ocularb0b/le3p/stls/manufactured/export_GantryCIdlers.stl

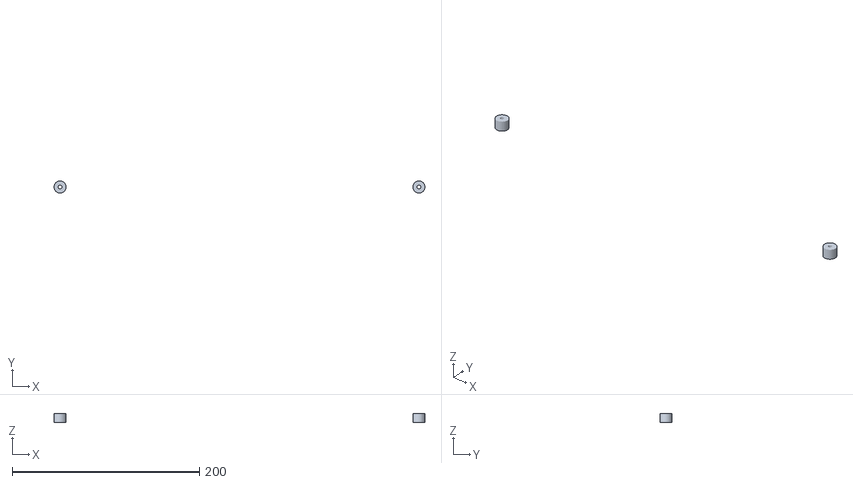
[picture p15: CAD file, 2014-03-09]
stls/manufactured/export_GantryCIdlers.stl
396.0 x 13.0 x 10.0
