ocularb0b/le3p/stls/printed/export_XCarriage.stl

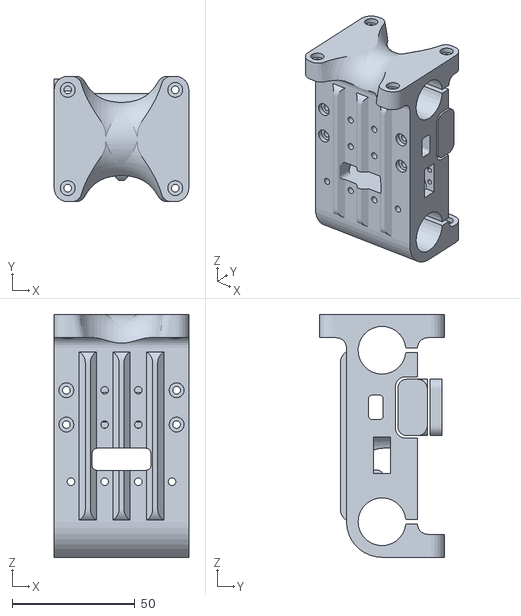
[picture p16: CAD file, 2014-02-16]
stls/printed/export_XCarriage.stl
55.0 x 51.2 x 99.2
