ocularb0b/le3p/stls/manufactured/export_GantryXBushings.stl

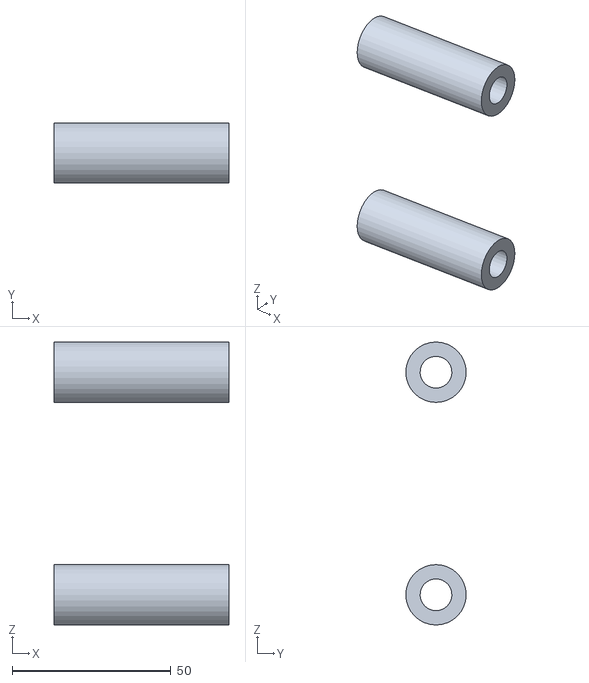
[picture p17: CAD file, 2014-03-09]
stls/manufactured/export_GantryXBushings.stl
55.0 x 19.0 x 89.0
