ocularb0b/le3p/stls/printed/export_XEnds.stl

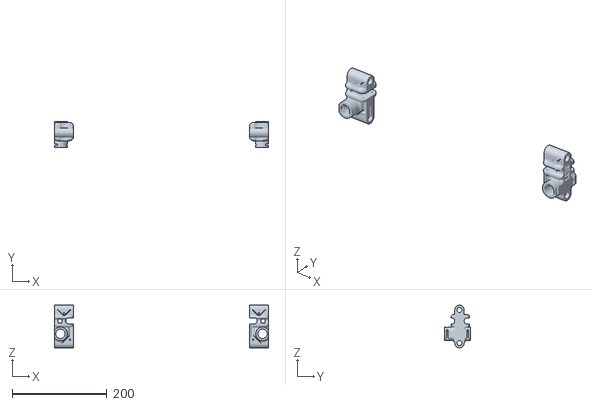
[picture p18: CAD file, 2014-02-16]
stls/printed/export_XEnds.stl
451.0 x 55.0 x 90.0
