ocularb0b/le3p/stls/manufactured/export_GantryMotors.stl

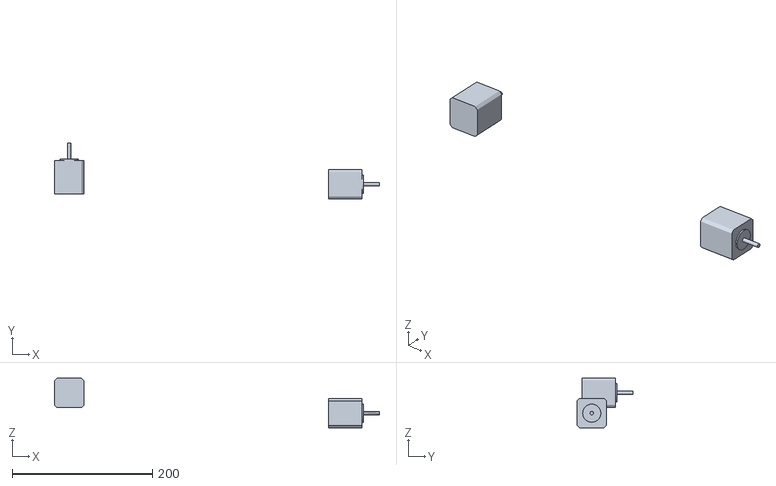
[picture p19: CAD file, 2014-03-09]
stls/manufactured/export_GantryMotors.stl
463.5 x 79.8 x 71.0
