ocularb0b/le3p/stls/printed/forprint_YEndsMotor.stl

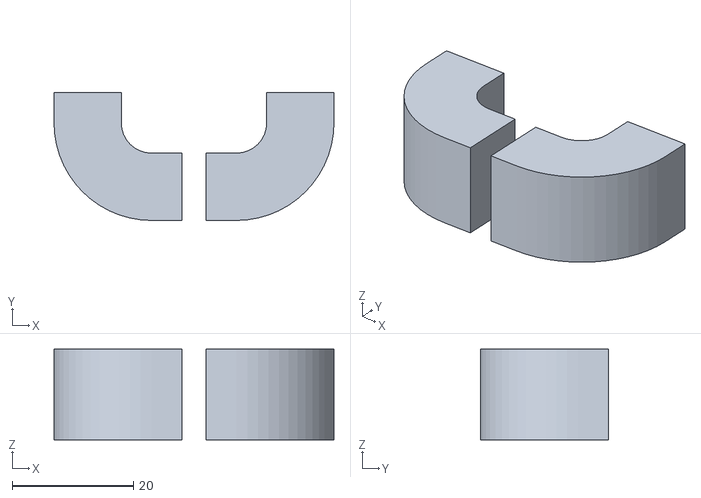
[picture p20: CAD file, 2013-11-06]
stls/printed/forprint_YEndsMotor.stl
46.2 x 21.1 x 15.0
