ocularb0b/le3p/stls/manufactured/export_GantryXRods.stl

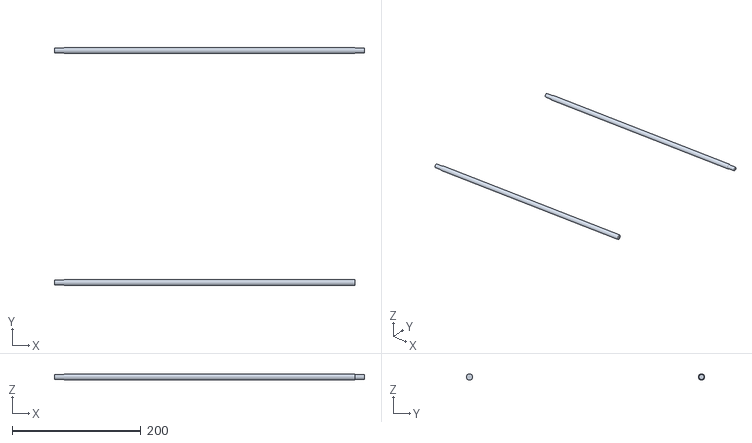
[picture p21: CAD file, 2014-03-09]
stls/manufactured/export_GantryXRods.stl
481.0 x 370.0 x 9.96
