ocularb0b/le3p/stls/printed/forprint_NozzleFanShroud.stl

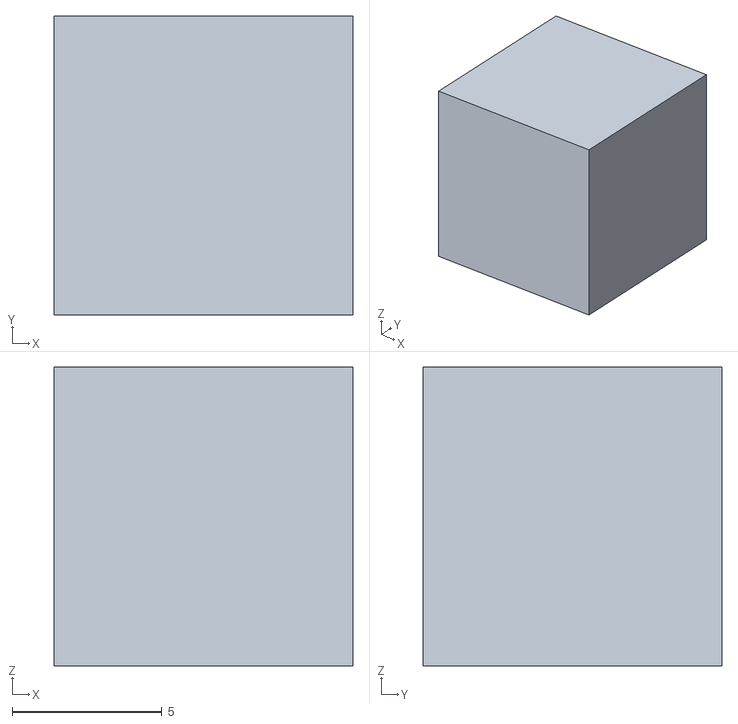
[picture p22: CAD file, 2013-11-01]
stls/printed/forprint_NozzleFanShroud.stl
10.0 x 10.0 x 10.0
