ocularb0b/le3p/stls/manufactured/export_ExtruderIdleBearing.stl

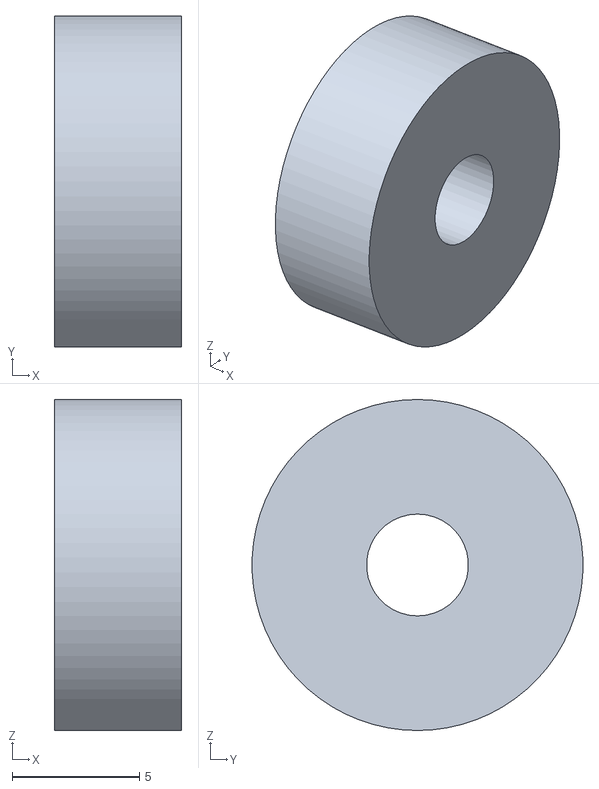
[picture p23: CAD file, 2014-03-09]
stls/manufactured/export_ExtruderIdleBearing.stl
5.00 x 13.0 x 13.0
