ocularb0b/le3p/stls/printed/export_DimmerMount.stl

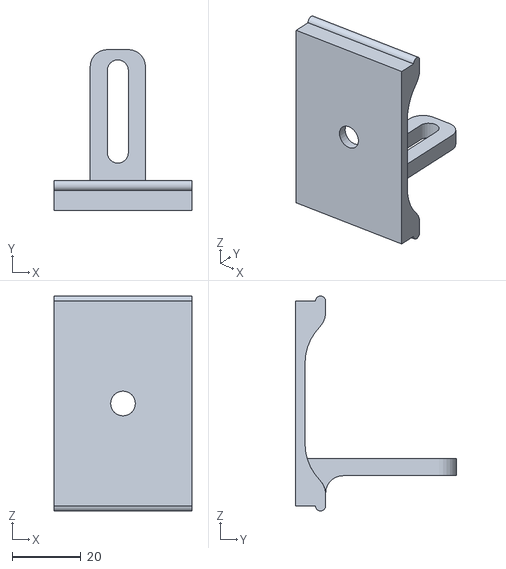
[picture p24: CAD file, 2013-10-20]
stls/printed/export_DimmerMount.stl
40.0 x 46.8 x 62.5
