ocularb0b/le3p/stls/manufactured/export_ExtruderDriveGear.stl

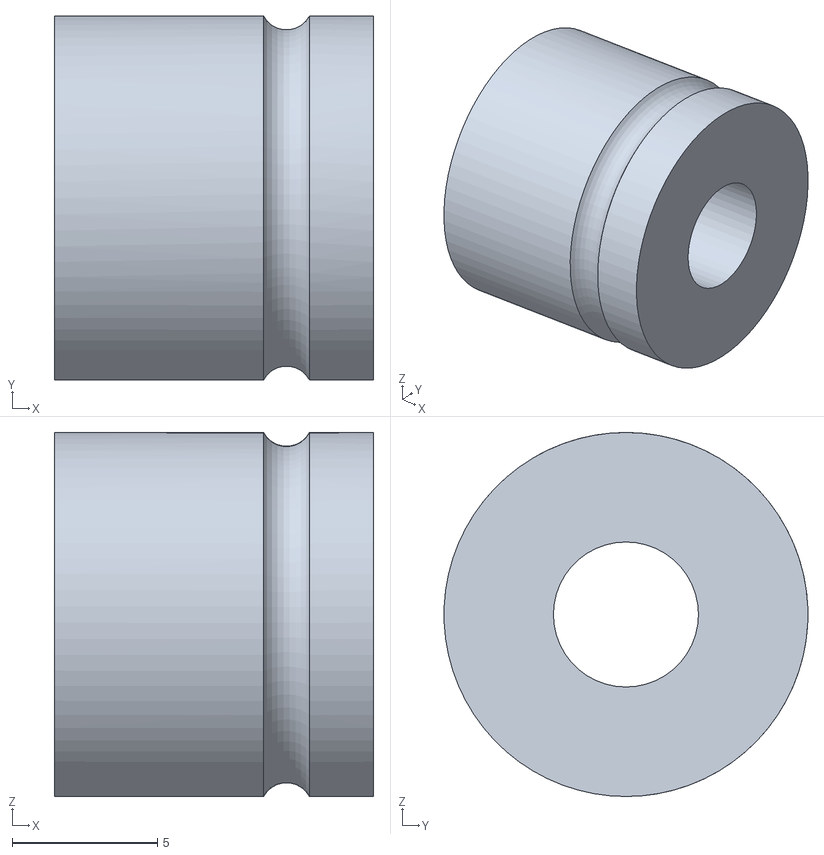
[picture p25: CAD file, 2014-03-09]
stls/manufactured/export_ExtruderDriveGear.stl
11.0 x 12.5 x 12.6
