ocularb0b/le3p/stls/printed/export_ControllerArm.stl

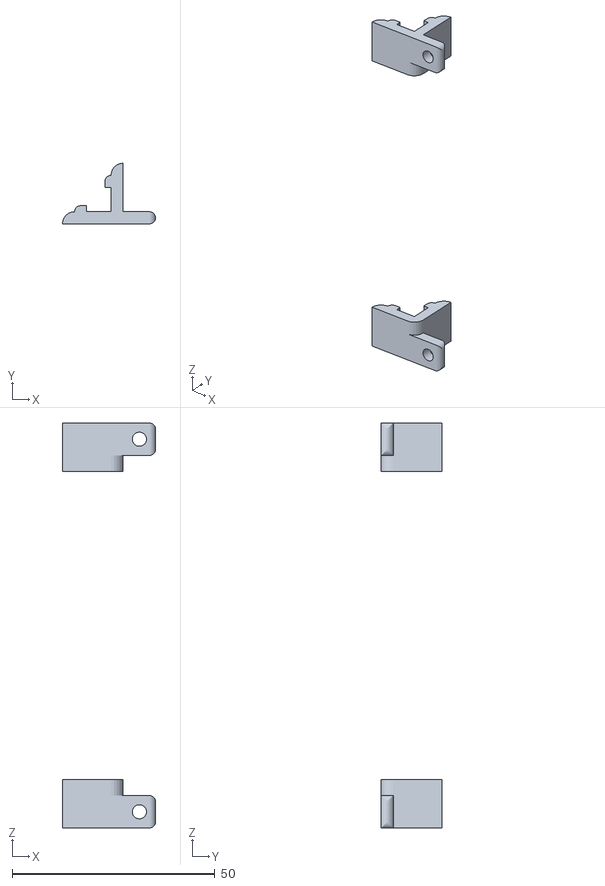
[picture p26: CAD file, 2013-10-20]
stls/printed/export_ControllerArm.stl
23.0 x 15.0 x 100.0
