ocularb0b/le3p/stls/manufactured/export_GantryYBushings.stl

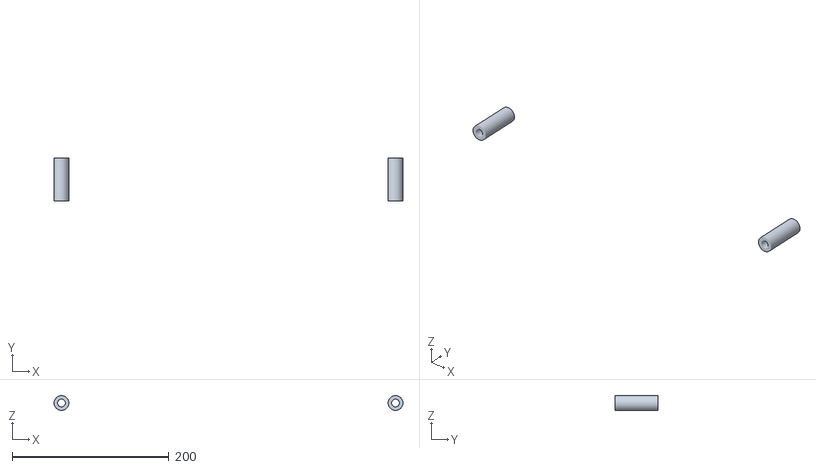
[picture p27: CAD file, 2014-03-09]
stls/manufactured/export_GantryYBushings.stl
445.0 x 55.0 x 19.0
