ocularb0b/le3p/stls/printed/export_LedBracket.stl

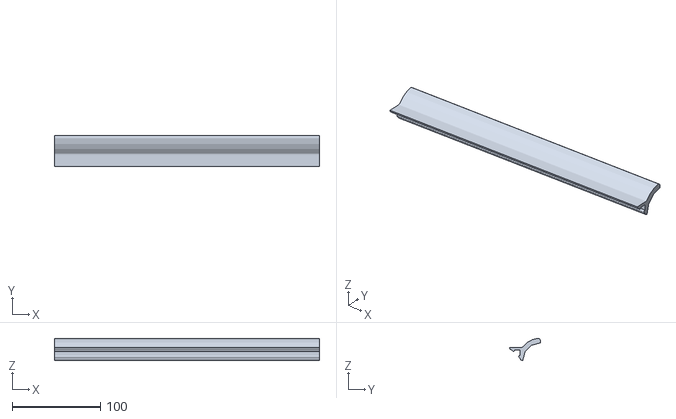
[picture p28: CAD file, 2013-10-20]
stls/printed/export_LedBracket.stl
300.0 x 35.2 x 25.3
