ocularb0b/le3p/stls/manufactured/export_GantryYRods.stl

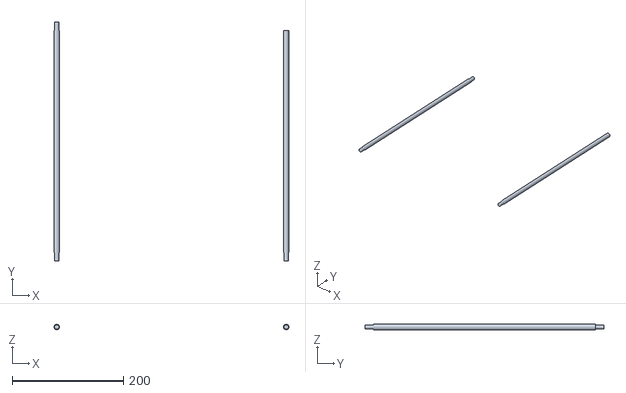
[picture p29: CAD file, 2014-03-09]
stls/manufactured/export_GantryYRods.stl
422.0 x 429.0 x 9.98
