ocularb0b/le3p/stls/printed/forprint_YStop.stl

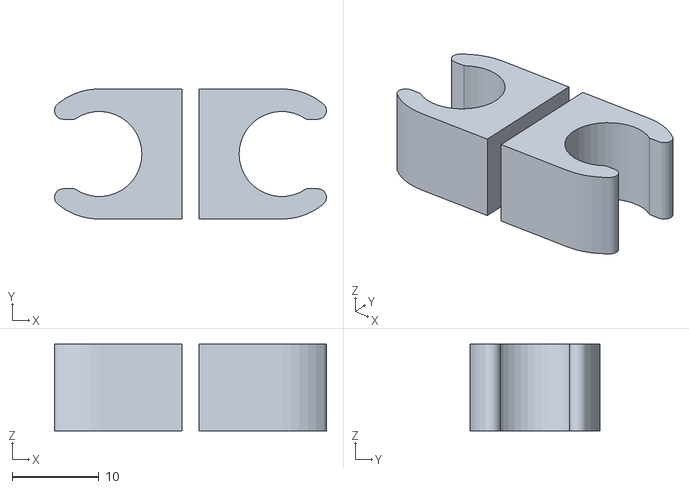
[picture p30: CAD file, 2013-10-20]
stls/printed/forprint_YStop.stl
31.3 x 15.0 x 10.0
