ocularb0b/le3p/stls/manufactured/export_ExtruderSupportBearing.stl

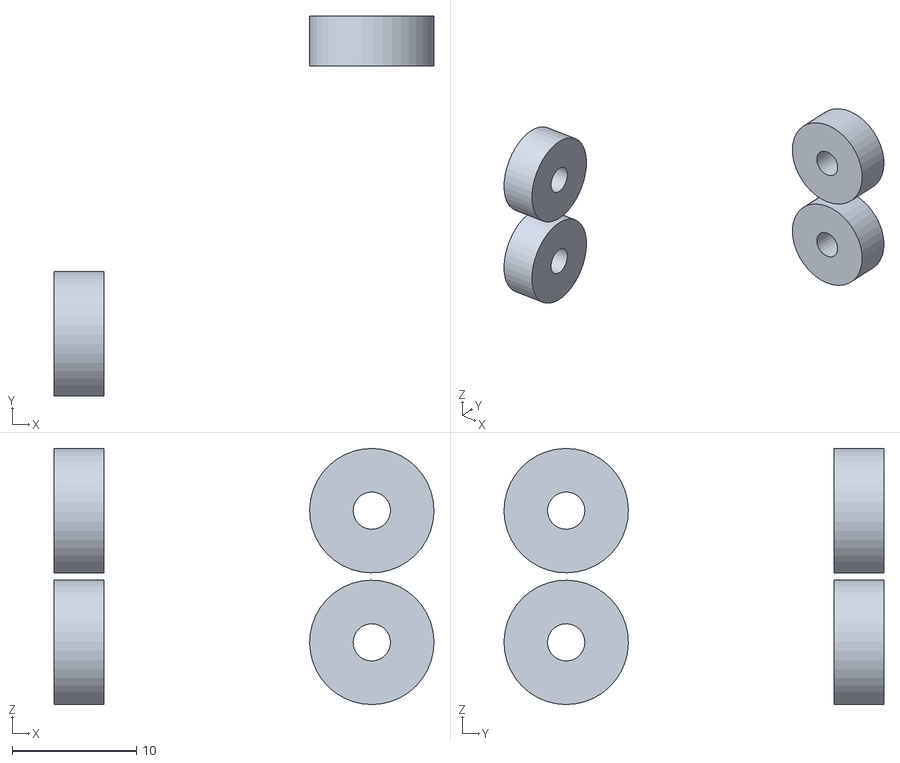
[picture p31: CAD file, 2013-10-20]
stls/manufactured/export_ExtruderSupportBearing.stl
30.5 x 30.5 x 20.6
