ocularb0b/le3p/stls/printed/forprint_ExtruderDriver.stl

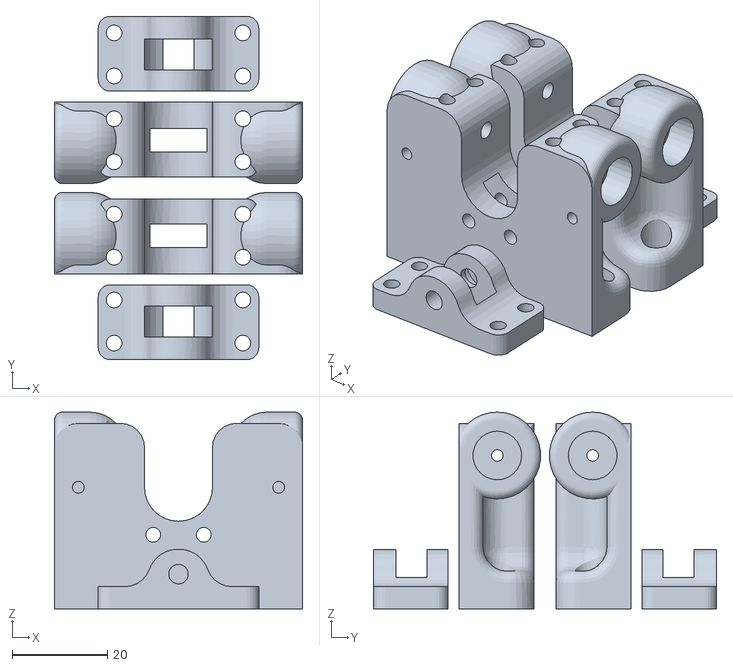
[picture p32: CAD file, 2013-10-20]
stls/printed/forprint_ExtruderDriver.stl
52.0 x 72.0 x 41.3
