ocularb0b/le3p/stls/manufactured/export_GantryBelt.stl

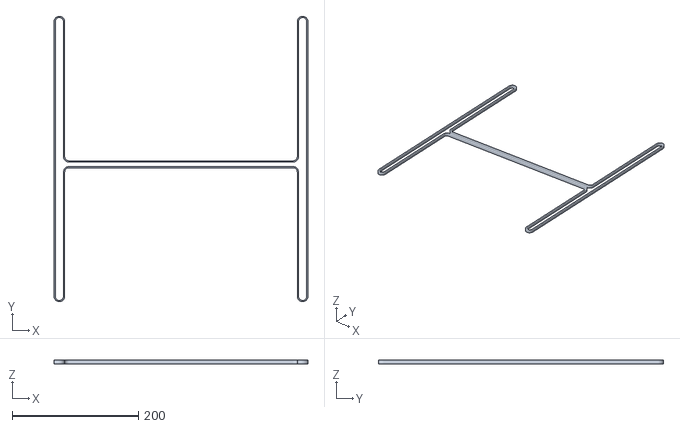
[picture p33: CAD file, 2013-10-18]
stls/manufactured/export_GantryBelt.stl
402.0 x 451.8 x 6.00
