ocularb0b/le3p/stls/printed/export_SmallCornerBrackets.stl

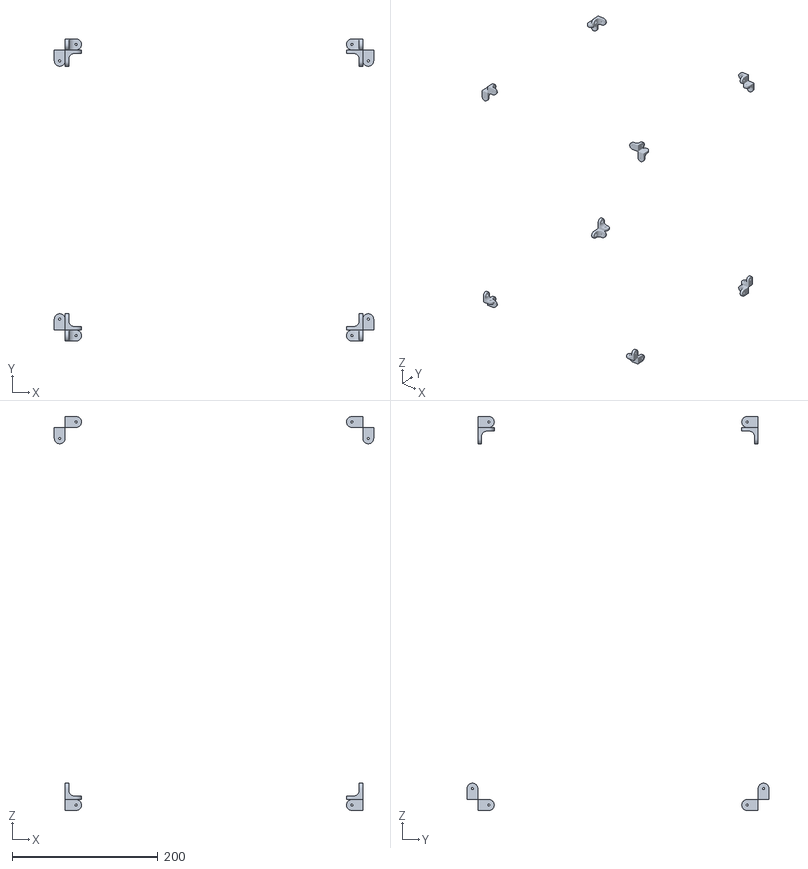
[picture p34: CAD file, 2013-10-20]
stls/printed/export_SmallCornerBrackets.stl
438.0 x 414.0 x 540.0
