ocularb0b/le3p/stls/manufactured/export_GantryZLeadNuts.stl

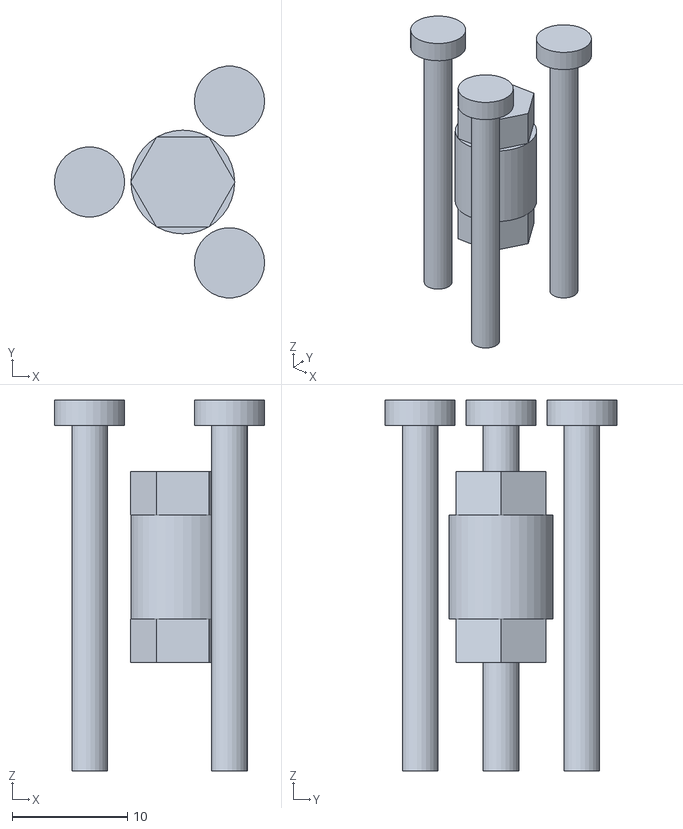
[picture p35: CAD file, 2013-10-18]
stls/manufactured/export_GantryZLeadNuts.stl
18.2 x 20.1 x 32.2
