ocularb0b/le3p/stls/printed/forprint_XEndsSet.stl

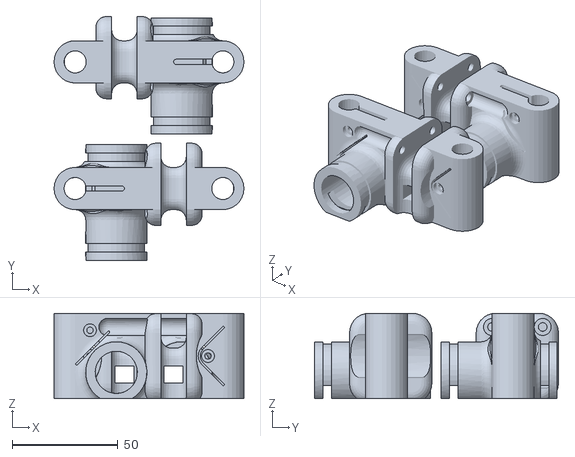
[picture p36: CAD file, 2013-10-20]
stls/printed/forprint_XEndsSet.stl
90.0 x 115.6 x 40.5
