ocularb0b/le3p/stls/manufactured/export_ZCouplers.stl

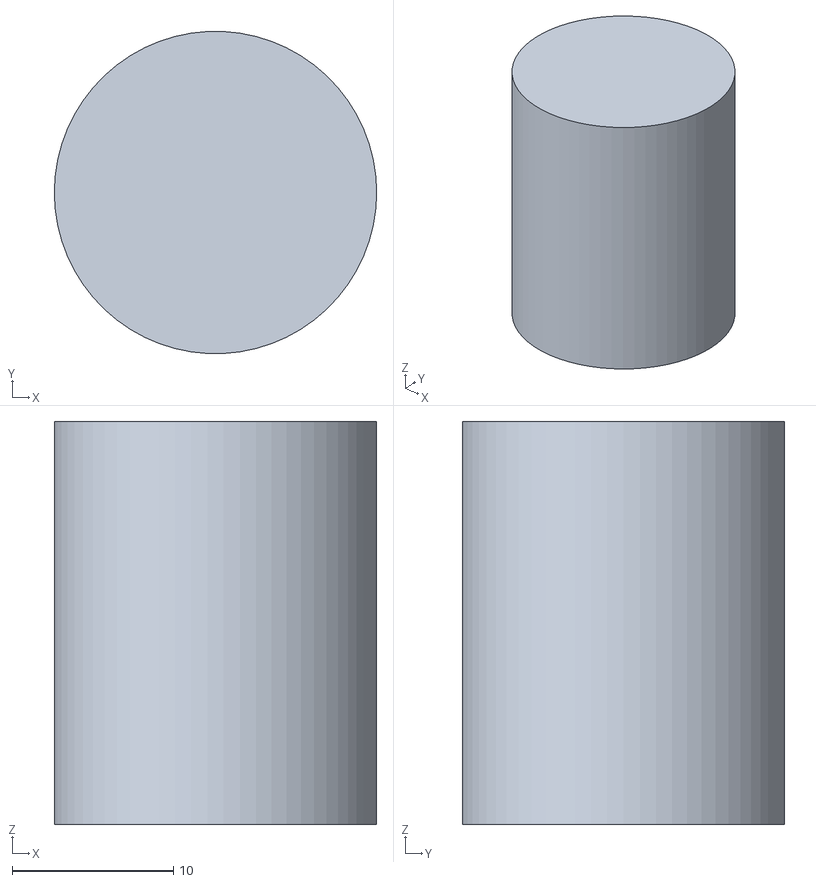
[picture p37: CAD file, 2013-10-18]
stls/manufactured/export_ZCouplers.stl
20.0 x 20.0 x 25.0
