ocularb0b/le3p/stls/printed/export_YEndsMotor.stl

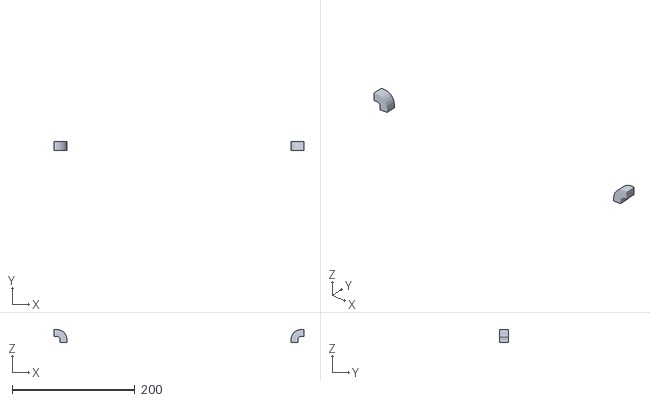
[picture p38: CAD file, 2013-10-20]
stls/printed/export_YEndsMotor.stl
408.0 x 15.0 x 21.1
