ocularb0b/le3p/stls/manufactured/export_ZMotors.stl

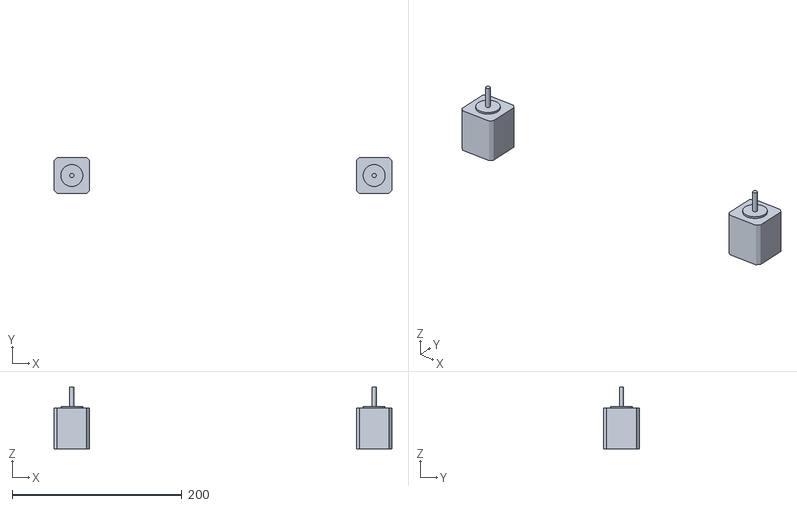
[picture p39: CAD file, 2013-10-18]
stls/manufactured/export_ZMotors.stl
398.0 x 42.0 x 73.0
