ocularb0b/le3p/stls/printed/export_YStop.stl

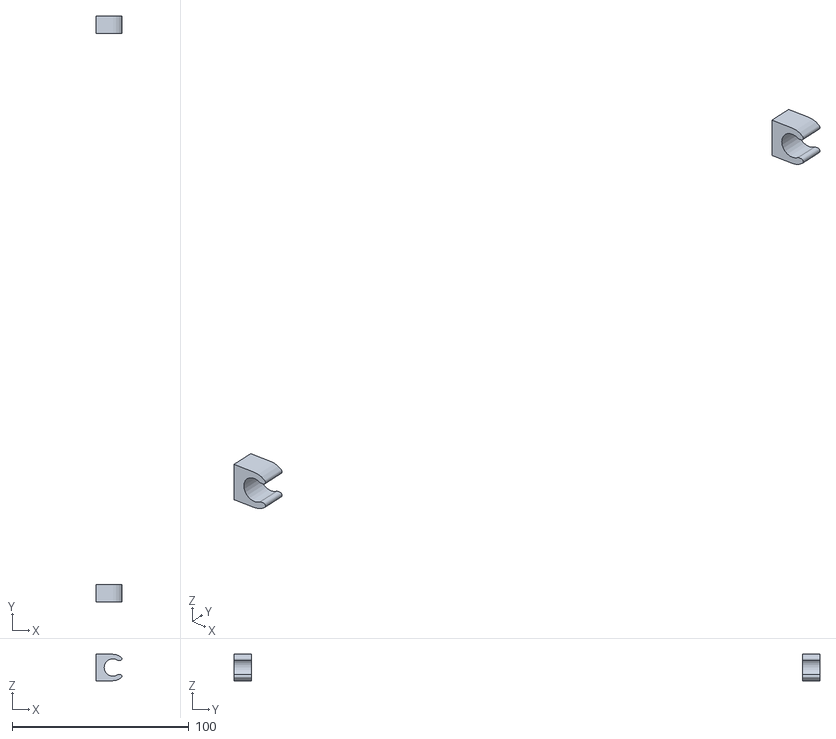
[picture p40: CAD file, 2013-10-20]
stls/printed/export_YStop.stl
14.7 x 331.5 x 15.0
