ocularb0b/le3p/stls/manufactured/export_GantryZBushings.stl

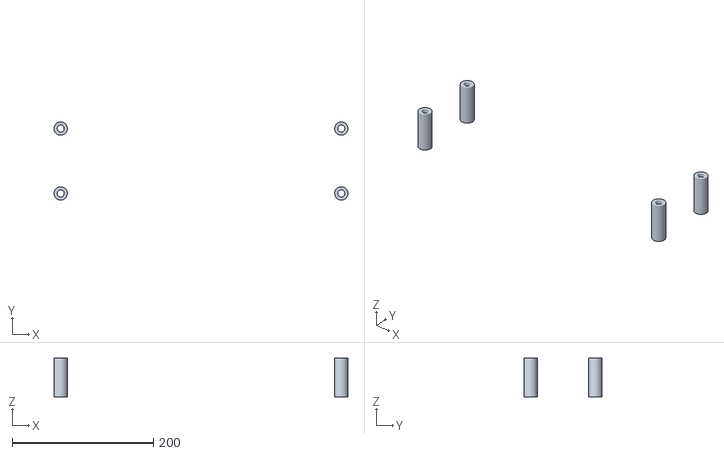
[picture p41: CAD file, 2013-07-04]
stls/manufactured/export_GantryZBushings.stl
417.0 x 111.0 x 55.0
