ocularb0b/le3p/stls/printed/forprint_ZMotorMounts.stl

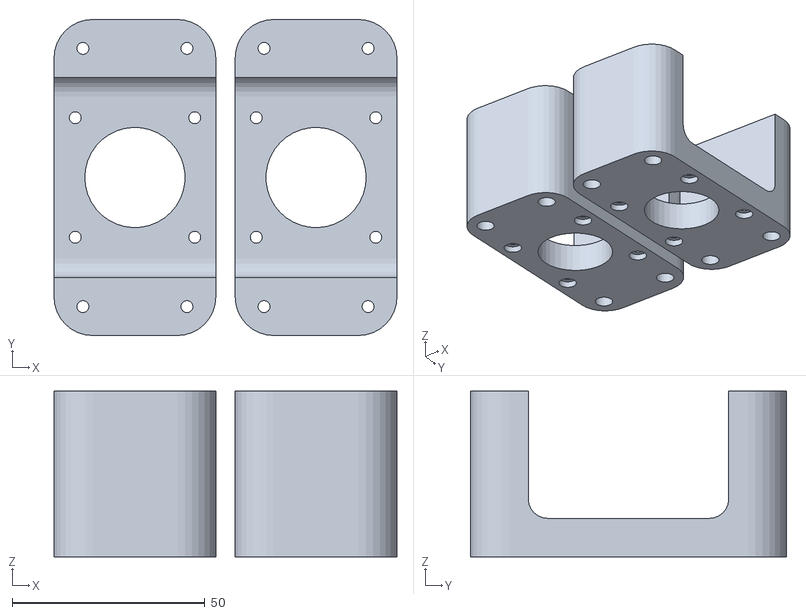
[picture p42: CAD file, 2013-10-20]
stls/printed/forprint_ZMotorMounts.stl
89.0 x 82.0 x 43.0
