ocularb0b/le3p/stls/printed/forprint_ToolHolder.stl

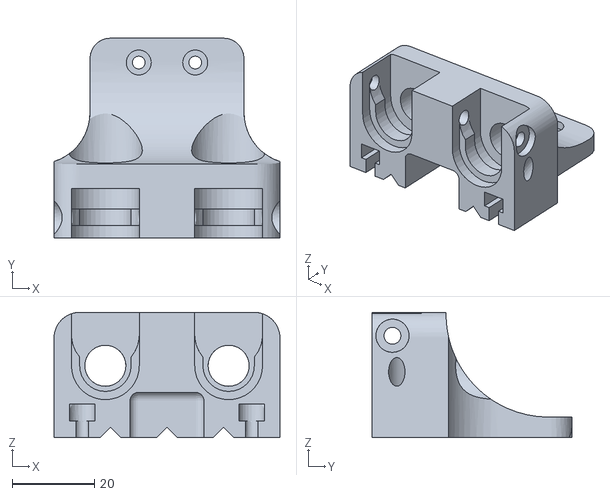
[picture p43: CAD file, 2013-10-20]
stls/printed/forprint_ToolHolder.stl
55.0 x 48.6 x 30.5
