ocularb0b/le3p/stls/printed/export_ZMotorMounts.stl

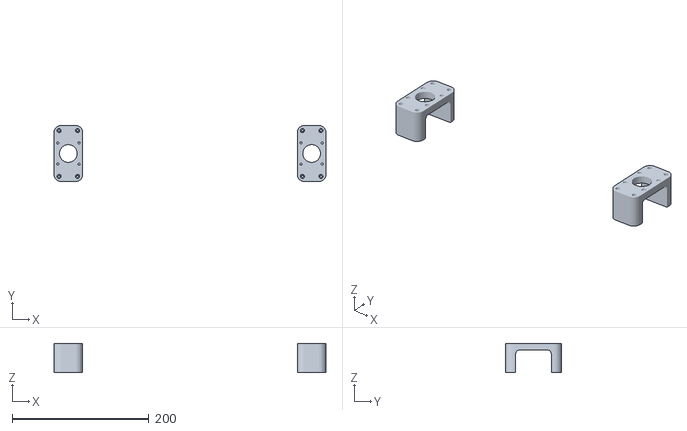
[picture p44: CAD file, 2013-10-20]
stls/printed/export_ZMotorMounts.stl
398.0 x 82.0 x 43.0
