ocularb0b/le3p/stls/printed/forprint_ZEnds.stl

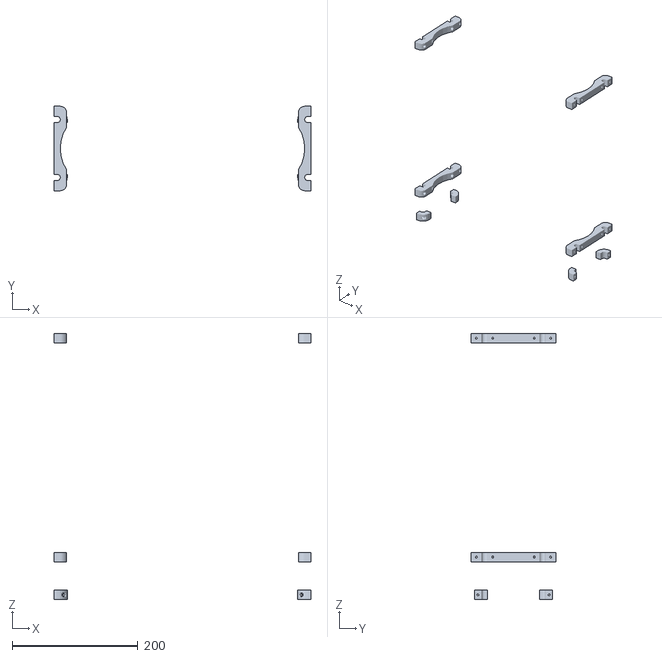
[picture p45: CAD file, 2013-10-18]
stls/printed/forprint_ZEnds.stl
408.0 x 134.2 x 422.5
