ocularb0b/le3p/stls/printed/export_ZCarriage.stl

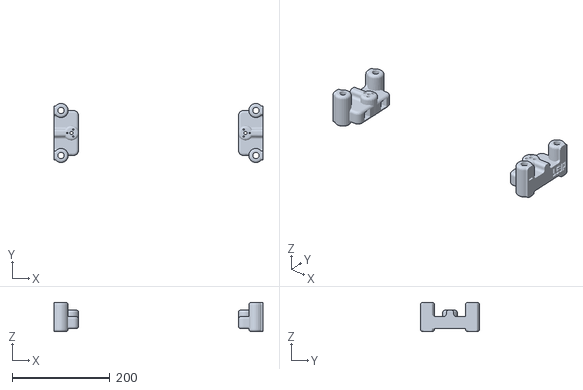
[picture p46: CAD file, 2013-10-18]
stls/printed/export_ZCarriage.stl
427.0 x 121.0 x 60.0
