ocularb0b/le3p/stls/printed/export_GantryMotorMounts.stl

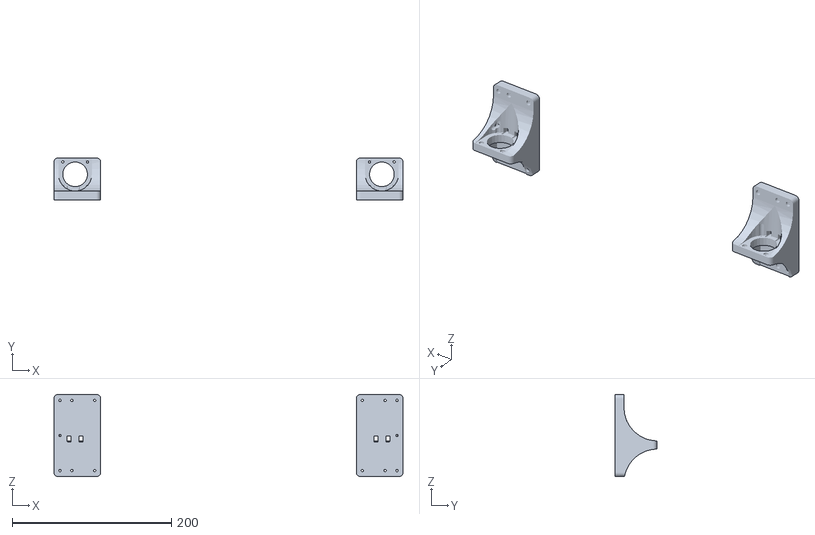
[picture p47: CAD file, 2013-10-18]
stls/printed/export_GantryMotorMounts.stl
438.0 x 52.8 x 103.0
