ocularb0b/le3p/stls/printed/export_YEndsIdle.stl

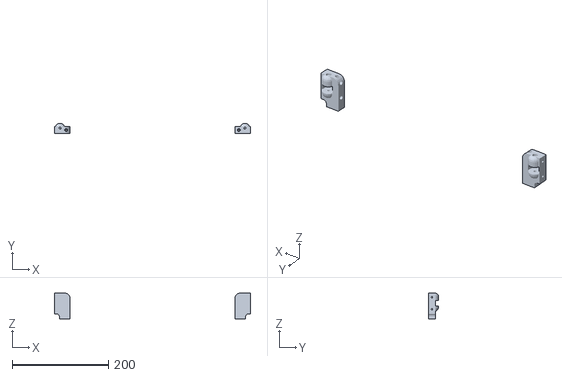
[picture p48: CAD file, 2013-10-18]
stls/printed/export_YEndsIdle.stl
408.0 x 21.5 x 53.3
