ocularb0b/le3p/stls/printed/forprint_YEndsIdle.stl

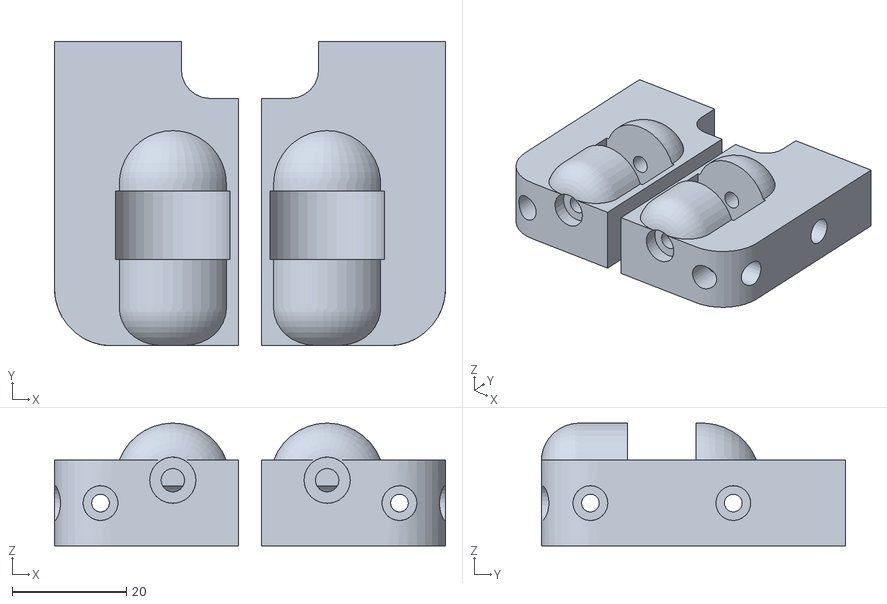
[picture p49: CAD file, 2013-10-18]
stls/printed/forprint_YEndsIdle.stl
68.4 x 53.3 x 21.5
