ocularb0b/le3p/stls/printed/forprint_ControllerArm.stl

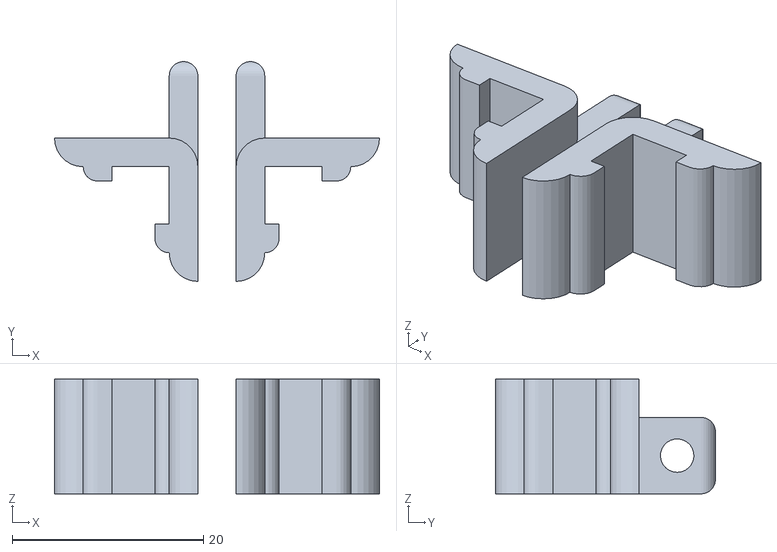
[picture p50: CAD file, 2013-09-15]
stls/printed/forprint_ControllerArm.stl
34.0 x 23.0 x 12.0
