ocularb0b/le3p/stls/printed/export_PowerSupplyMounts.stl

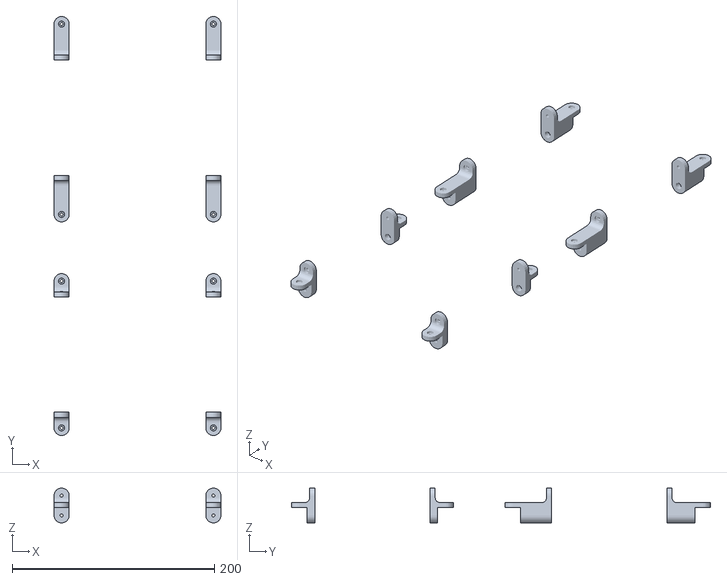
[picture p51: CAD file, 2013-09-15]
stls/printed/export_PowerSupplyMounts.stl
165.0 x 414.0 x 34.5
