ocularb0b/le3p/include/parts.py

#le3p-v0.1.3 Parts functions

# le3p - A larger envelope, t-slot extrusion based, H-Gantry 3D printer.
#
# Copyright (c) 2013 Scott Maher scott.a.maher@gmail.com
#
# This file is part of le3p

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
from __future__ import division
import sys

import FreeCAD, Part, math
from FreeCAD import Base
from FreeCAD import Vector
from math import pi, cos, sin

from include.shapes import regPolygon

def BoxExtrusion(size=5, length=40):
  
	blank=Part.makeBox(length, size, size)
	blank.translate(Vector(0, -size, -size))
	
	slota=Part.makeBox(length, size/6, size/3)
	slota.translate(Vector(0, -size/2 - (size/12), -size))
	cut1 = blank.cut(slota)
	
	slotb=Part.makeBox(length, size/6, size/3)
	slotb.translate(Vector(0, -size/2 - (size/12), -size/3))
	cut2 = cut1.cut(slotb)
	
	slotc=Part.makeBox(length, size/3, size/6)
	slotc.translate(Vector(0, -size/3, -size/12 -size/2))
	cut3 = cut2.cut(slotc)
		
	slotd=Part.makeBox(length, size/3, size/6)
	slotd.translate(Vector(0, -size, -size/12 -size/2))
	cut4 = cut3.cut(slotd)
	cut4.translate(Vector(0, size/2, size/2))
		
	return cut4

def CapHeadScrew(l=10,d=3,hd=6,hh=3,cut=0):
	s = Part.makeCylinder(d/2,l)
	s.translate(Vector(0,0,-l))
	if cut == 0:
		h = Part.makeCylinder(hd/2,hh)
		
	if cut == 1:
		h = Part.makeCylinder(hd/2,hh+hd+l)
		h = h.makeFillet(hd/2-0.01,[h.Edges[0]])
	
	screw=s.fuse(h)	
	return screw

def NemaMotor(motor=[]):
	bodyblank = Part.makeBox(motor[0], motor[0], motor[1])
	body = bodyblank.makeChamfer(motor[0]/12, [bodyblank.Edges[0], bodyblank.Edges[2], bodyblank.Edges[4],  bodyblank.Edges[6]])
	body.translate(Vector(-motor[0]/2, -motor[0]/2, -motor[1]))
	face = Part.makeCylinder(motor[5]/2, 2)
	shaft = Part.makeCylinder(motor[2]/2, motor[3])
	fuse1 = face.fuse(shaft)
	motor = body.fuse(fuse1)
	return motor

def TimingGear(pitchdia=25, gearwidth=12, boredia=5,hubdia = 20, hubheight = 6):
	g = Part.makeCylinder(pitchdia/2, gearwidth)
	hb = Part.makeCylinder(hubdia/2, hubheight)
	hb.translate(Vector(0, 0, -hubheight))
	f1 = g.fuse(hb)
	b = Part.makeCylinder(boredia/2, gearwidth + hubheight)
	b.translate(Vector(0, 0, -hubheight))
	c1 = f1.cut(b)
	c1.translate(Vector(0,0,-gearwidth/2))
	tg = c1
	return tg

def StraightBushing(dim=[10,20,20]):
	bo = Part.makeCylinder(dim[1]/2,dim[2])
	bi = Part.makeCylinder(dim[0]/2,dim[2])
	b = bo.cut(bi)
	return b

def BronzeBushing10mm():
	od1 = 15
	od2 = 17
	fd = 17.5
	ft = 1
	ind = 10
	l = 10
	
	bb = Part.makeCone(od1/2,od2/2,l)
	th = Part.makeCylinder(ind/2,l)
	fl = Part.makeCylinder(fd/2,ft)
	
	b = bb.fuse(fl)
	b = b.cut(th)
	return b

def SleaveBushing10mm():
	od1 = 12
	od2 = 13
	ind = 10
	l = 10
	
	bb = Part.makeCone(od1/2,od2/2,l)
	th = Part.makeCylinder(ind/2,l)
	b = bb.cut(th)
	return b

def Bearing(dim=[4,13,5]):
	bo = Part.makeCylinder(dim[1]/2,dim[2])
	bi = Part.makeCylinder(dim[0]/2,dim[2])
	b = bo.cut(bi)
	return b

def Fan(size=40,thick=10.75,screwdia=3.25,screwspacing=32):
	
	fb = Part.makeBox(size,thick,size)
	fb = fb.makeFillet(screwdia,[fb.Edges[1],fb.Edges[3],fb.Edges[5],fb.Edges[7]])
	
	#port
	pt = Part.makeCylinder(size/2-(size*0.02),thick)
	pt.rotate(Vector(0,0,0),Vector(1,0,0),-90)
	pt.translate(Vector(size/2,0,size/2))
	
	#screws
	sc = Part.makeCylinder(screwdia/2,thick)
	sc.rotate(Vector(0,0,0),Vector(1,0,0),-90)
	sc.translate(Vector(size/2,0,size/2))
	
	s1=sc.copy()
	s1.translate(Vector(-screwspacing/2,0,-screwspacing/2))
	s2=sc.copy()
	s2.translate(Vector(-screwspacing/2,0,screwspacing/2))
	s3=sc.copy()
	s3.translate(Vector(screwspacing/2,0,screwspacing/2))
	s4=sc.copy()
	s4.translate(Vector(screwspacing/2,0,-screwspacing/2))
	
	sc=s1.fuse(s2.fuse(s3).fuse(s4))
	
	#fanhub
	fh = Part.makeCylinder(size/4,thick)
	fh.rotate(Vector(0,0,0),Vector(1,0,0),-90)
	fh.translate(Vector(size/2,0,size/2))
	
	#fan blades
	n = 7
	bth = 1
	bl = Part.makeBox(bth,thick*2,size/2)
	bl.translate(Vector(-bth/2,-thick,0))
	bl.rotate(Vector(0,0,0),Vector(0,0,1),-45)
	bl.translate(Vector(size/2,thick/2,size/2))
	bls = bl.copy()
	for i in range(1,n):
		b=bl.copy()
		b.rotate(Vector(size/2,0,size/2),Vector(0,1,0),(360/n)*i)
		bls=bls.fuse(b)
	blsfc = Part.makeBox(size+20,thick,size+20)
	blsfc.translate(Vector(-10,-thick+2,-10))
	bls = bls.cut(blsfc)
	blsfc.translate(Vector(0,thick*2-4,0))
	bls = bls.cut(blsfc)
	blset = Part.makeCylinder(size/2-(size*0.016),thick)
	blset.rotate(Vector(0,0,0),Vector(1,0,0),-90)
	blset.translate(Vector(size/2,0,size/2))
	bls = bls.common(blset)
	
	fan = fb.cut(pt)
	fan = fan.cut(sc)
	fan = fan.fuse(fh)
	fan = fan.fuse(bls)
	return fan

def Kraken():
	xsize = 40
	ysize = 35
	zsize = 20
	msoffset = 3
	msdia = 3
	msoffset = 3
	msdeep = 10
	whdia = 8.5
	whoffset = 10
	whdeep = 15
	fhdia = 8
	fhoffset = 7.5
	nheight = 5.5
	ndia = 8
	nnutheight = 3
	nconeheight = 2
	hbrdia = 2.8
	hhbx = 16
	hhby = 16
	hhbz = 12
	hhboffset = 4
	
	hbheight = 20
	
	bb = Part.makeBox(xsize,ysize,zsize)
	bb.translate(Vector(-xsize/2,-ysize/2,0))
	
	ms = Part.makeCylinder(msdia/2,msdeep)
	ms.translate(Vector(xsize/2-msoffset,ysize/2-msoffset,zsize - msdeep))
	ms = ms.fuse(ms.mirror(Vector(0,0,0),Vector(1,0,0)))
	ms = ms.fuse(ms.mirror(Vector(0,0,0),Vector(0,1,0)))
	
	wh = Part.makeCylinder(whdia/2,whdeep)
	wh.translate(Vector(xsize/2 - whoffset,0,zsize - whdeep))
	wh = wh.fuse(wh.mirror(Vector(0,0,0),Vector(1,0,0)))
	
	fh = Part.makeCylinder(fhdia/2,zsize)
	fh.translate(Vector(xsize/2 - whoffset,ysize/2 - fhoffset,2))
	fh = fh.fuse(fh.mirror(Vector(0,0,0),Vector(1,0,0)))
	fh = fh.fuse(fh.mirror(Vector(0,0,0),Vector(0,1,0)))
	
	hhb = Part.makeBox(hhbx,hhby,hhbz)
	hhb.translate(Vector(-hhbx/2,-hhbx+hhboffset,0))
	hhbhb = Part.makeCylinder(hbrdia/2,5)
	hhbhb.translate(Vector(0,0,hhbz))
	hhb = hhb.fuse(hhbhb)
	hhb.translate(Vector(xsize/2 - whoffset,ysize/2 - fhoffset,0))
	hhb = hhb.fuse(hhb.mirror(Vector(0,0,0),Vector(1,0,0)))
	hhbr2 = hhb.copy()
	hhbr2.translate(Vector(0,fhoffset*2 - ysize,0))
	hhb = hhb.fuse(hhbr2)
	hhb.translate(Vector(0,0,nheight))
	
	nzc = Part.makeCone(0.6,3,nconeheight)
	nzn = regPolygon(6,ndia/2,extrude = nnutheight)
	nzn.translate(Vector(0,0,nconeheight))
	nzs = Part.makeCylinder(3,10)
	nzs.translate(Vector(0,0,nconeheight+nnutheight))
	
	nz = nzc.fuse(nzn.fuse(nzs))
	nz.translate(Vector(xsize/2 - whoffset,ysize/2 - fhoffset,0))
	nz = nz.fuse(nz.mirror(Vector(0,0,0),Vector(1,0,0)))
	nz = nz.fuse(nz.mirror(Vector(0,0,0),Vector(0,1,0)))
	
	hb = bb.cut(ms)
	hb = hb.cut(wh)
	hb = hb.cut(fh)
	hb.translate(Vector(0,0,hbheight))
	
	kraken = hb.fuse(hhb)
	kraken = kraken.fuse(nz)
	
	return kraken
	

def E3Dv4():
	blockx = 14
	blocky = 20
	blockz = 10
	fin=2.1
	findia=25
	b1t=4.7
	b2t=4.6
	b3t=5
	b4t=fin*10
	b11t=fin*6
	b16t=5
	#built top up (upside down)
	b1 = Part.makeCylinder(8,b1t)
	#
	b2 = Part.makeCylinder(6,b1t+b2t+fin*2)
	#
	b3 = Part.makeCylinder(8,b3t)
	b3.translate(Vector(0,0,b1t+b2t))
	#
	b31 = Part.makeCylinder(8,fin)
	b31.translate(Vector(0,0,b1t+b2t+b3t+fin))
	#
	b4 = Part.makeCylinder(8.93/2,b4t+fin*2)
	b4.translate(Vector(0,0,b1t+b2t+b3t))
	#
	b5 = Part.makeCylinder(findia/2,fin)
	b5.translate(Vector(0,0,b1t+b2t+b3t+fin*3))
	#
	b6 = Part.makeCylinder(findia/2,fin)
	b6.translate(Vector(0,0,b1t+b2t+b3t+fin*5))
	#
	b7 = Part.makeCylinder(findia/2,fin)
	b7.translate(Vector(0,0,b1t+b2t+b3t+fin*7))
	#
	b8 = Part.makeCylinder(findia/2,fin)
	b8.translate(Vector(0,0,b1t+b2t+b3t+fin*9))
	#
	b9 = Part.makeCylinder(13/2,fin)
	b9.translate(Vector(0,0,b1t+b2t+b3t+fin*8))
	#
	b10 = Part.makeCylinder(findia/2,fin)
	b10.translate(Vector(0,0,b1t+b2t+b3t+fin*11))
	#
	b11 = Part.makeCylinder(15/2,b11t)
	b11.translate(Vector(0,0,b1t+b2t+b3t+fin*11))
	#
	b12 = Part.makeCylinder(findia/2,fin)
	b12.translate(Vector(0,0,b1t+b2t+b3t+fin*13))
	#
	b13 = Part.makeCylinder(findia/2,fin)
	b13.translate(Vector(0,0,b1t+b2t+b3t+fin*15))
	#
	b14 = Part.makeCylinder(findia/2,fin)
	b14.translate(Vector(0,0,b1t+b2t+b3t+fin*17))
	#
	b15 = Part.makeCylinder(2.8/2,fin)
	b15.translate(Vector(0,0,b1t+b2t+b3t+fin*19))
	#
	b16 = Part.makeCylinder(3,b16t)
	b16.translate(Vector(0,0,b1t+b2t+b3t+fin*19-b16t))
	#
	blk=Part.makeBox(blockx,blocky,blockz)
	blk.translate(Vector(-blockx/2,-blocky+blockx/2,b1t+b2t+b3t+fin*19))
	#
	noz = Part.makeCone(6,0.5,6)
	noz.translate(Vector(0,0,b1t+b2t+b3t+fin*19+blockz))
	
	he = b1.fuse(b2.fuse(b3.fuse(b31.fuse(b4.fuse(b5.fuse(b6.fuse(b7.fuse(b8.fuse(b9.fuse(b10.fuse(b11.fuse(b12.fuse(b13.fuse(b14.fuse(b15.fuse(b16.fuse(blk.fuse(noz))))))))))))))))))
	he.rotate(Vector(0,0,0),Vector(1,0,0),180)
	return he
	
